JulianFP/CO2-Sensor/Gallery/Back.jpg

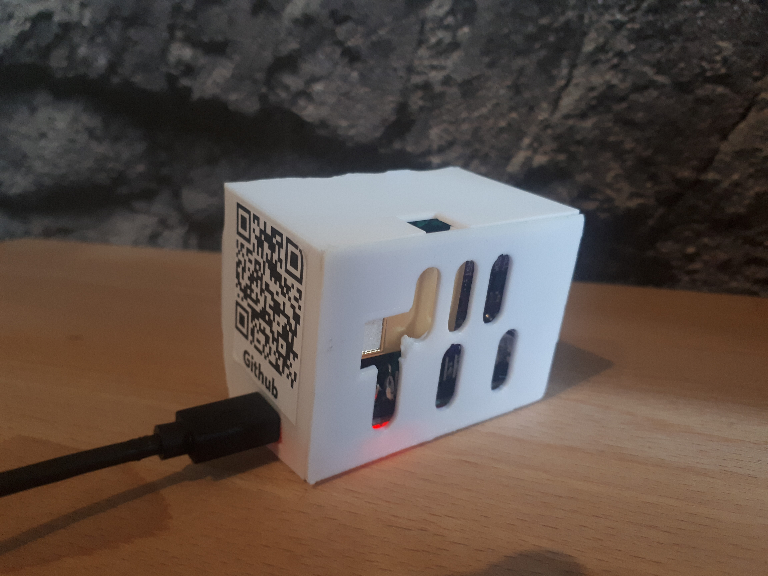
Gallery/Back.jpg
