JulianFP/CO2-Sensor/Gallery/Front.jpg

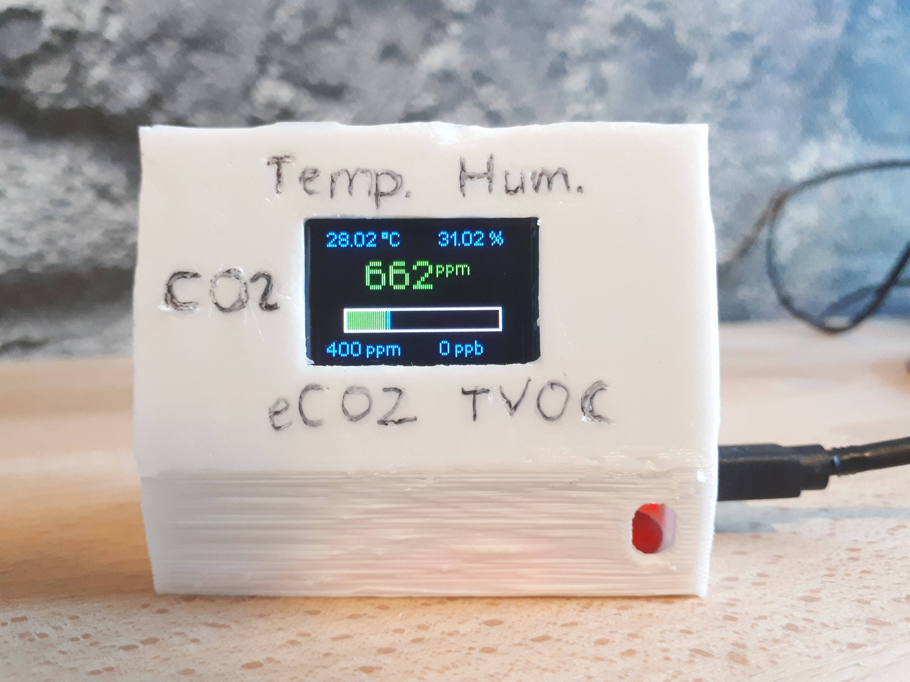
Gallery/Front.jpg
