JulianFP/CO2-Sensor/Gallery/soldered_back_withmodules.jpg

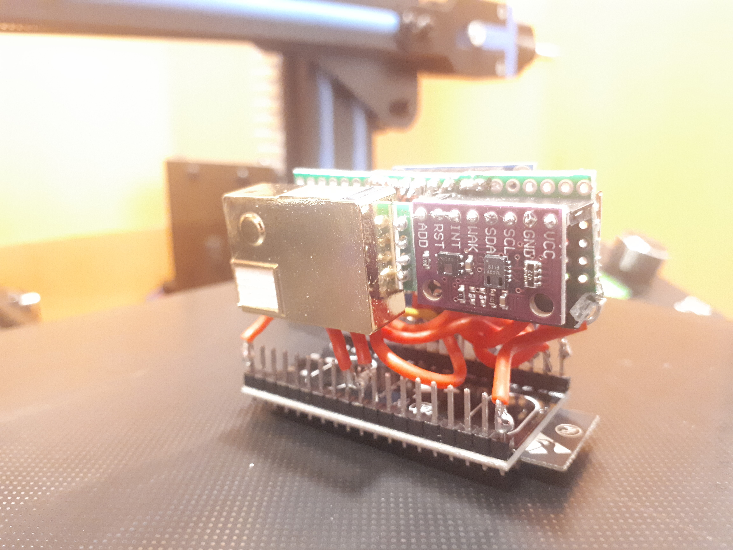
Gallery/soldered_back_withmodules.jpg
