JulianFP/CO2-Sensor/Gallery/soldered_front_withmodules.jpg

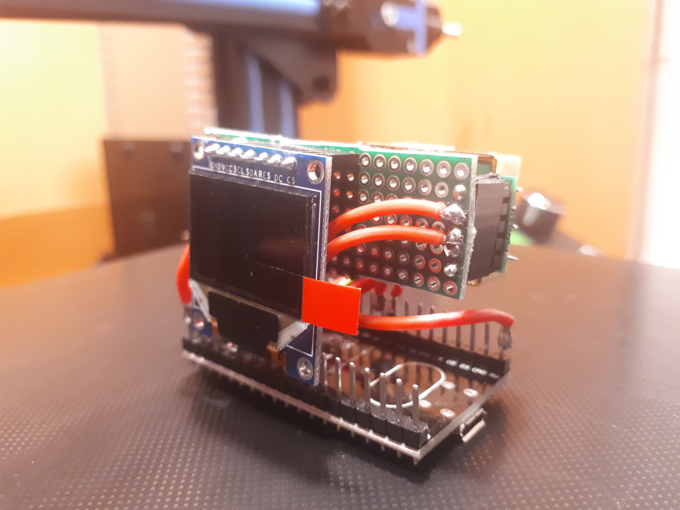
Gallery/soldered_front_withmodules.jpg
